TinyCircuits/TinyCircuits-TinyViolin-ASM4003/examples/TinyViolinR1/generator.py

# -*- coding: cp1252 -*-
songList = [
  "MacGyver:d=4,o=6,b=150:8b4,8e5,8a5,8b5,a5,8e5,8b4,8p,8e5,8a5,8b5,8a5,8e5,b4,8p,8e5,8a5,8b5,a5,8e5,8b4,8p,8a5,8d,8c,8d,8c,8b5,8a5,8b4,8e5,8a5,8b5,a5,8e5,8b4,8p,8e5,8a5,8b5,8a5,8e5,b4,8p,8e5,8a5,8b5,a5,8e5,8b4,8p,8a5,8d,8c,8d,8c,8b5,8a5,b5,8p,2b5,8p,b5,8p,a5,d.,b5,8p,2b5,8p,8b5,8p,2a5,p,8c,8c,8c,8c,8c,8c,2b5,16p,8f#5,8a5,8p,2g5,8p,8c,8c,8p,b5,8a5,8b5,8a5,8g5,8p,e,2a5,16p,8c,8c,8p,2b5,8p,8f#5,8a5,8p,2g5,8p,8c,8c,8p,4b5,8a5,8b5,8a5,8g5,8p,4e,2a5,2b5,32p,8c,8b5,8a5,c,8b5,8a5,8d,8c,8b5,d,8c,8b5,e,8d,8e,f#,b5,g,8p,f#,f,b5,8g,8e,8b5,8f#,8d,8a5,8e,8c,8g5,8d,8b5,8g5,8c,8e5,8b5,8d5,8c,8b5,8a5,8g5,a#5,a5,8g,8g5,8d,8g5,8d#,8d#5,8a#5,8a5,8g5,8g4,8d5,8g4,8d#5,8g4,8a#4,8a4,8g4,8g4,8g4,8g4,8g4,8g4,8g4"  ,
  "The Simpsons:d=4,o=5,b=160:c.6,e6,f#6,8a6,g.6,e6,c6,8a,8f#,8f#,8f#,2g,8p,8p,8f#,8f#,8f#,8g,a#.,8c6,8c6,8c6,c6"  ,
  "Indiana:d=4,o=5,b=250:e,8p,8f,8g,8p,1c6,8p.,d,8p,8e,1f,p.,g,8p,8a,8b,8p,1f6,p,a,8p,8b,2c6,2d6,2e6,e,8p,8f,8g,8p,1c6,p,d6,8p,8e6,1f.6,g,8p,8g,e.6,8p,d6,8p,8g,e.6,8p,d6,8p,8g,f.6,8p,e6,8p,8d6,2c6"  ,
  "TakeOnMe:d=4,o=4,b=160:8f#5,8f#5,8f#5,8d5,8p,8b,8p,8e5,8p,8e5,8p,8e5,8g#5,8g#5,8a5,8b5,8a5,8a5,8a5,8e5,8p,8d5,8p,8f#5,8p,8f#5,8p,8f#5,8e5,8e5,8f#5,8e5,8f#5,8f#5,8f#5,8d5,8p,8b,8p,8e5,8p,8e5,8p,8e5,8g#5,8g#5,8a5,8b5,8a5,8a5,8a5,8e5,8p,8d5,8p,8f#5,8p,8f#5,8p,8f#5,8e5,8e5"  ,
  "Entertainer:d=4,o=5,b=140:8d,8d#,8e,c6,8e,c6,8e,2c.6,8c6,8d6,8d#6,8e6,8c6,8d6,e6,8b,d6,2c6,p,8d,8d#,8e,c6,8e,c6,8e,2c.6,8p,8a,8g,8f#,8a,8c6,e6,8d6,8c6,8a,2d6"  ,
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
]

import os
from random import SystemRandom

def main():
    output = open('songs.h', 'wb')
    songNum = SystemRandom()
    output.write("#include <inttypes.h>\n")
    output.write("#include <avr/pgmspace.h>\n")
    for i in range(10) :
        output.write("const char song_%d[] PROGMEM = \"%s\";" % (i,songList[songNum.randrange(len(songList))]))
        output.write('\n')
    output.close()

 
if __name__ == "__main__":
    main()
